Oliver0804/ESP32_SpaceRat/pic/2022-03-03_10.38.25.png

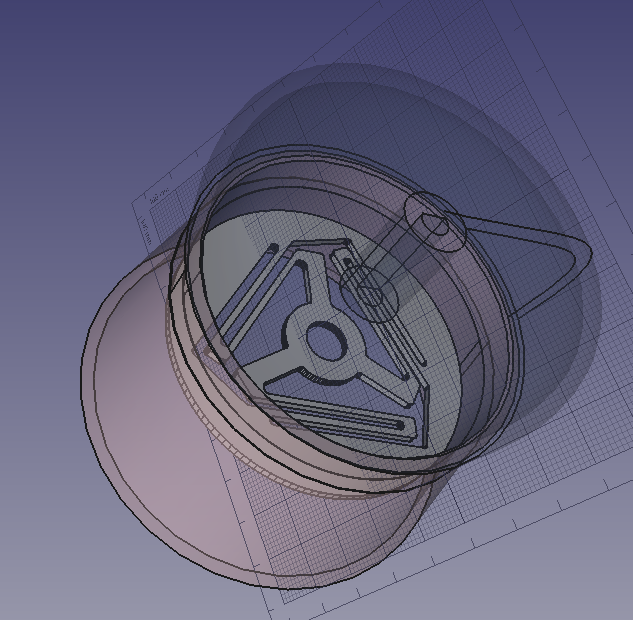
pic/2022-03-03_10.38.25.png
