Oliver0804/ESP32_SpaceRat/pic/截圖 2022-03-03 下午11.47.40.png

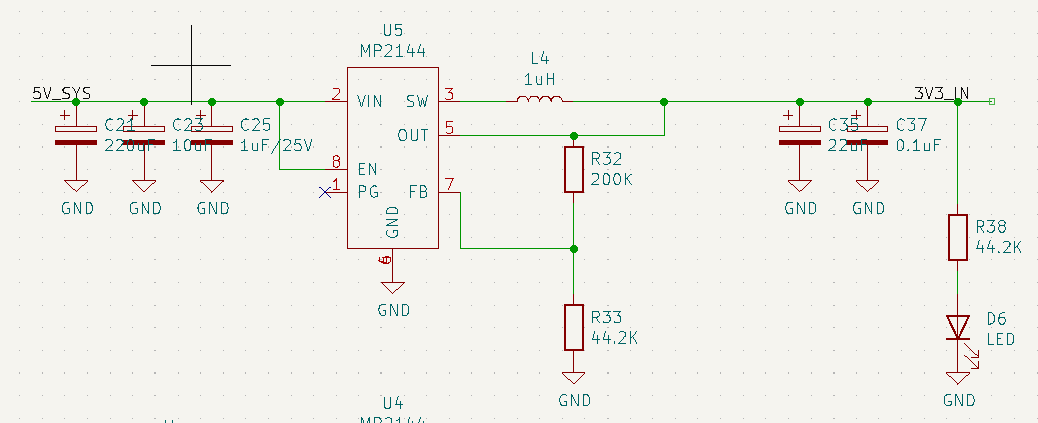
pic/截圖 2022-03-03 下午11.47.40.png
