Oliver0804/ESP32_SpaceRat/Datasheet/ESP32-DEVKIT-v1-DOIT-Pinout-Getting-Started-1024x773.webp

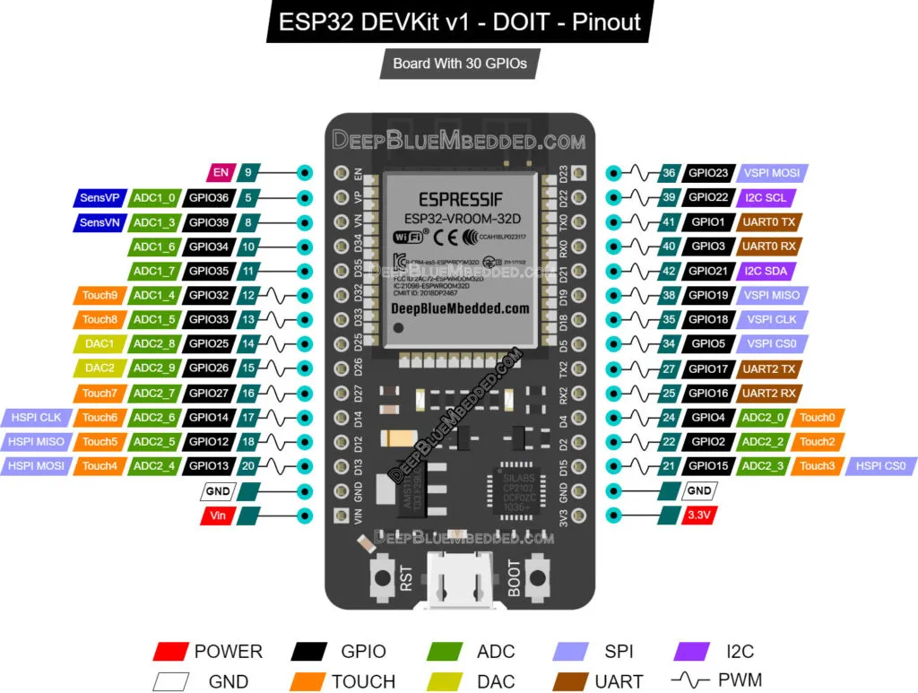
Datasheet/ESP32-DEVKIT-v1-DOIT-Pinout-Getting-Started-1024x773.webp
